scshsy/GPU-USB-PWM-Fan-Controller/RTX6000D散热方案/img2.jpg

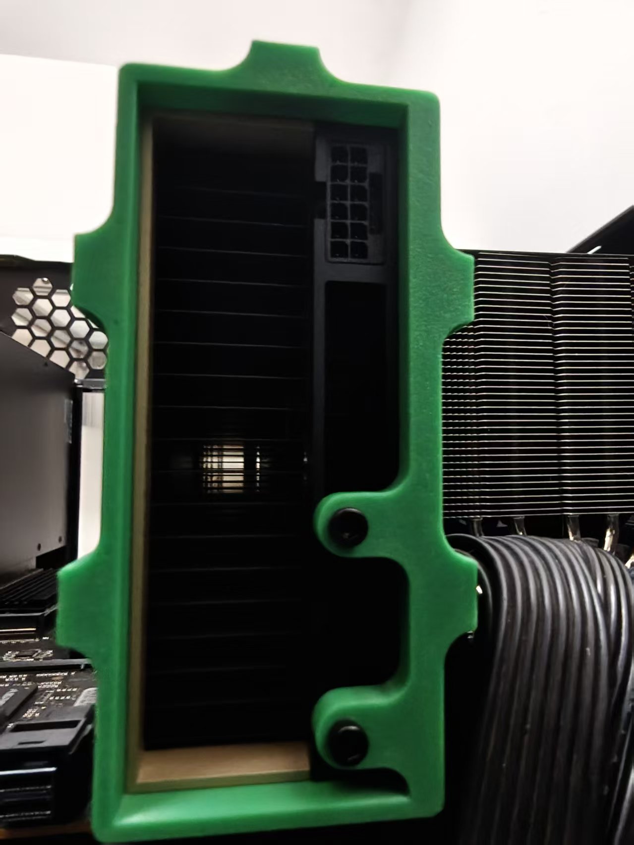
RTX6000D散热方案/img2.jpg
